sparkfun/SparkFun_Thing_Plus_DA16200/docs/img/hookup_guide/assembly_batt.jpg

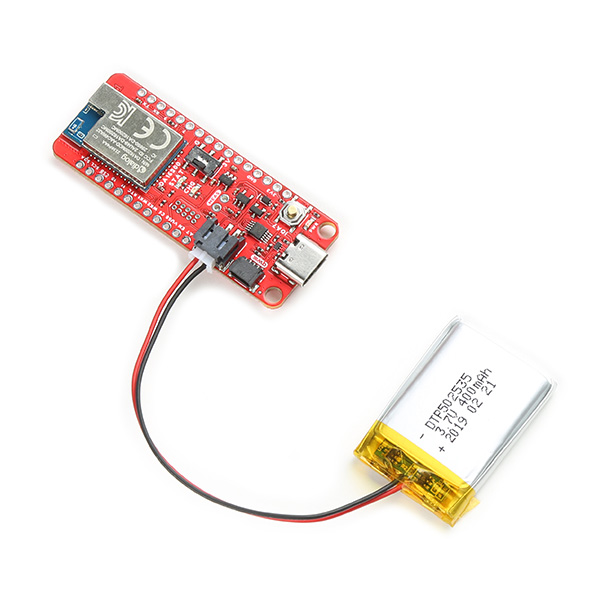
docs/img/hookup_guide/assembly_batt.jpg
