sparkfun/SparkFun_Thing_Plus_DA16200/docs/img/hookup_guide/assembly_headers.jpg

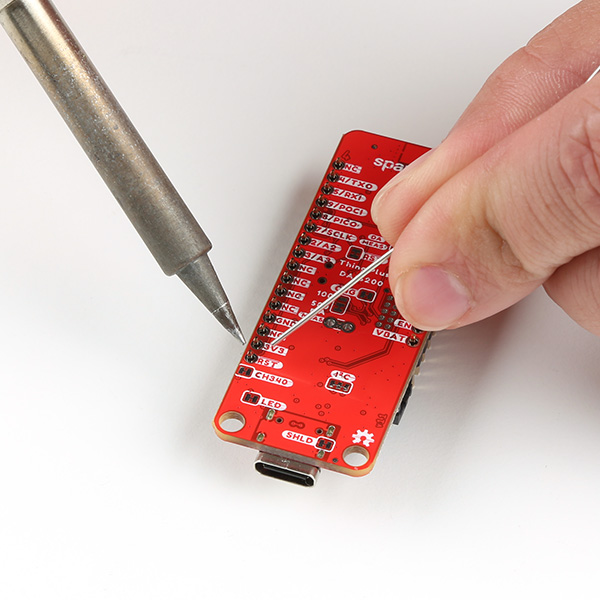
docs/img/hookup_guide/assembly_headers.jpg
