sparkfun/SparkFun_Thing_Plus_DA16200/docs/img/hookup_guide/assembly_jtag_program.jpg

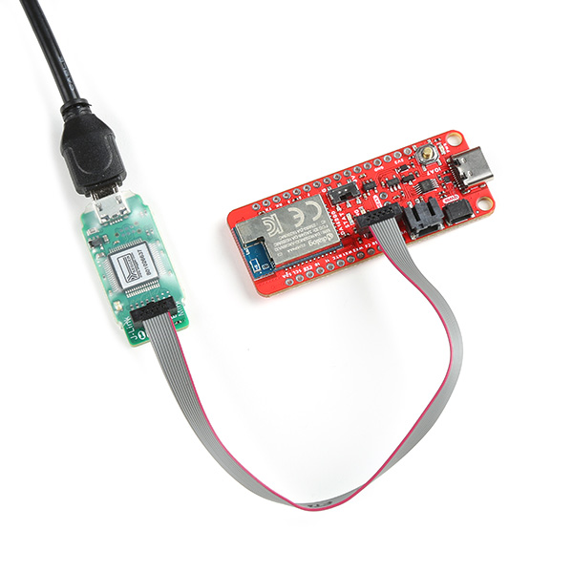
docs/img/hookup_guide/assembly_jtag_program.jpg
