sparkfun/SparkFun_Thing_Plus_DA16200/docs/img/hookup_guide/asssembly_qwiic.jpg

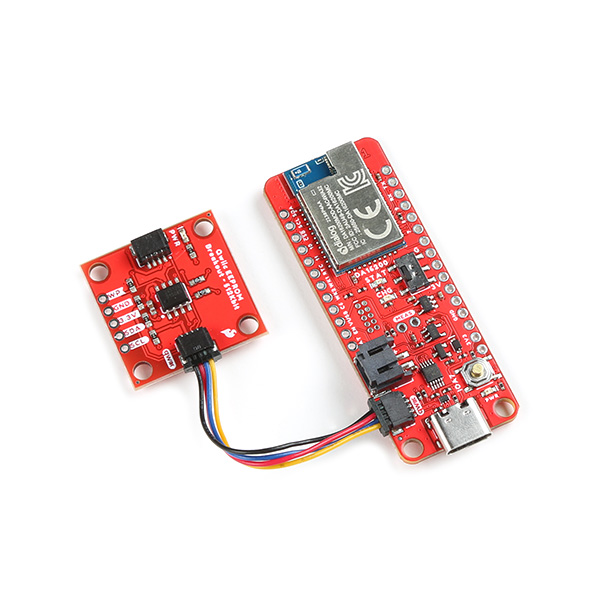
docs/img/hookup_guide/asssembly_qwiic.jpg
