sparkfun/SparkFun_Thing_Plus_DA16200/docs/img/hookup_guide/DA16200- 03.jpg

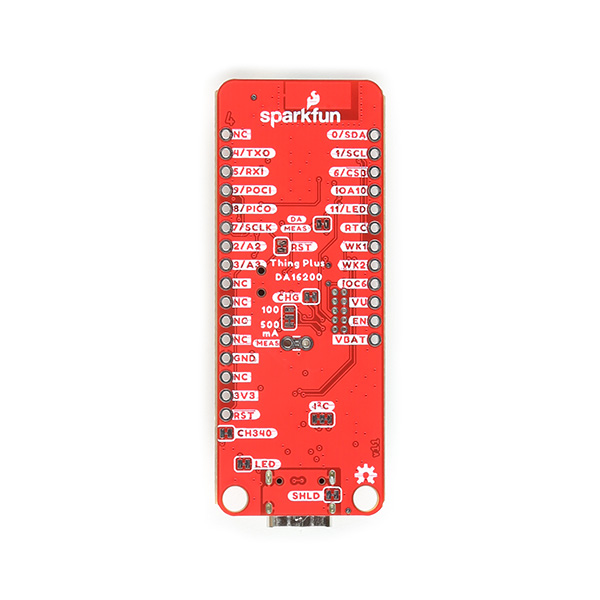
docs/img/hookup_guide/DA16200- 03.jpg
