sparkfun/SparkFun_Thing_Plus_DA16200/docs/img/hookup_guide/DA16200-_02.jpg

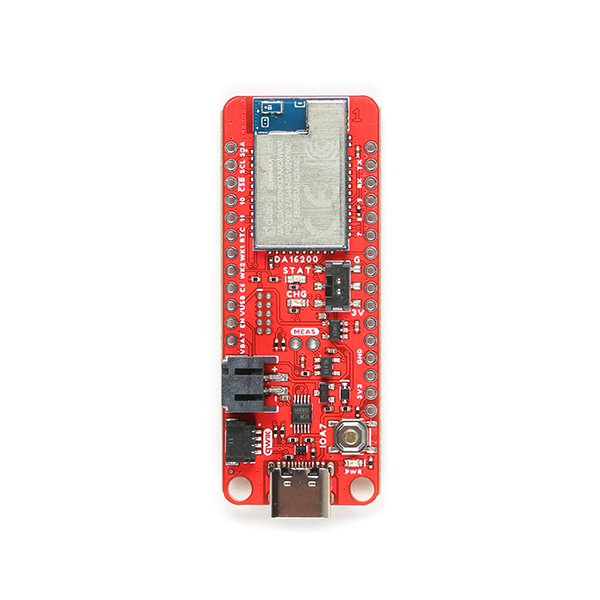
docs/img/hookup_guide/DA16200-_02.jpg
