sparkfun/SparkFun_Thing_Plus_DA16200/docs/img/hookup_guide/DA16200_thing_plus-jumpers.jpg

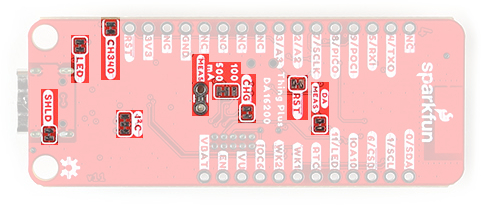
docs/img/hookup_guide/DA16200_thing_plus-jumpers.jpg
