sparkfun/SparkFun_Thing_Plus_DA16200/docs/img/hookup_guide/dimensions.png

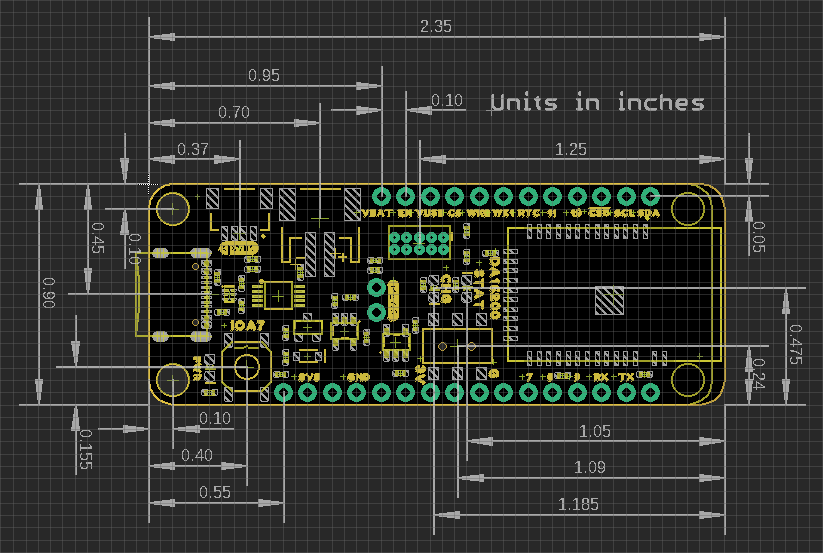
docs/img/hookup_guide/dimensions.png
