sparkfun/SparkFun_Thing_Plus_DA16200/docs/img/hookup_guide/jumper_caution-small.jpg

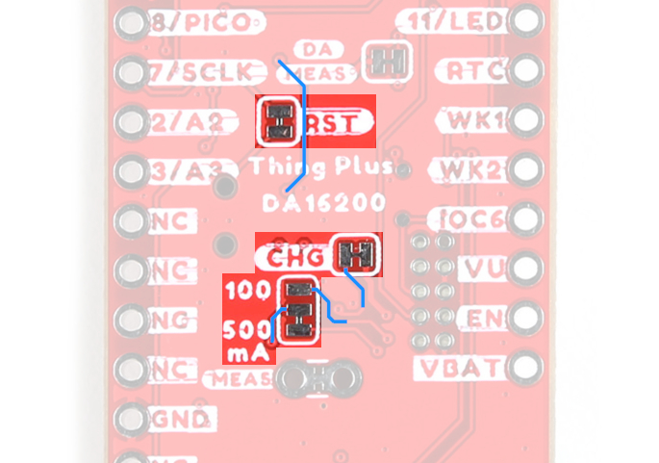
docs/img/hookup_guide/jumper_caution-small.jpg
