sparkfun/SparkFun_Thing_Plus_DA16200/docs/img/sdk_guide/build_project.gif

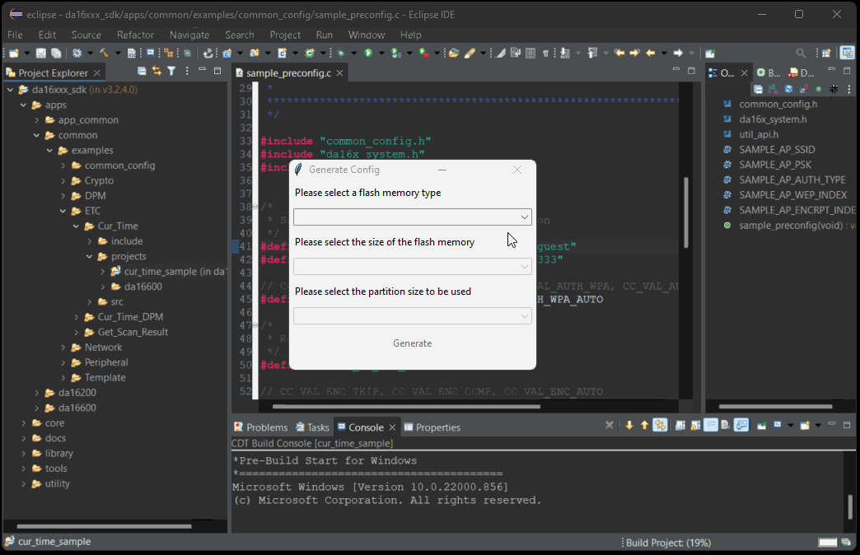
docs/img/sdk_guide/build_project.gif
