sparkfun/SparkFun_Thing_Plus_DA16200/docs/img/sdk_guide/download_firmware.png

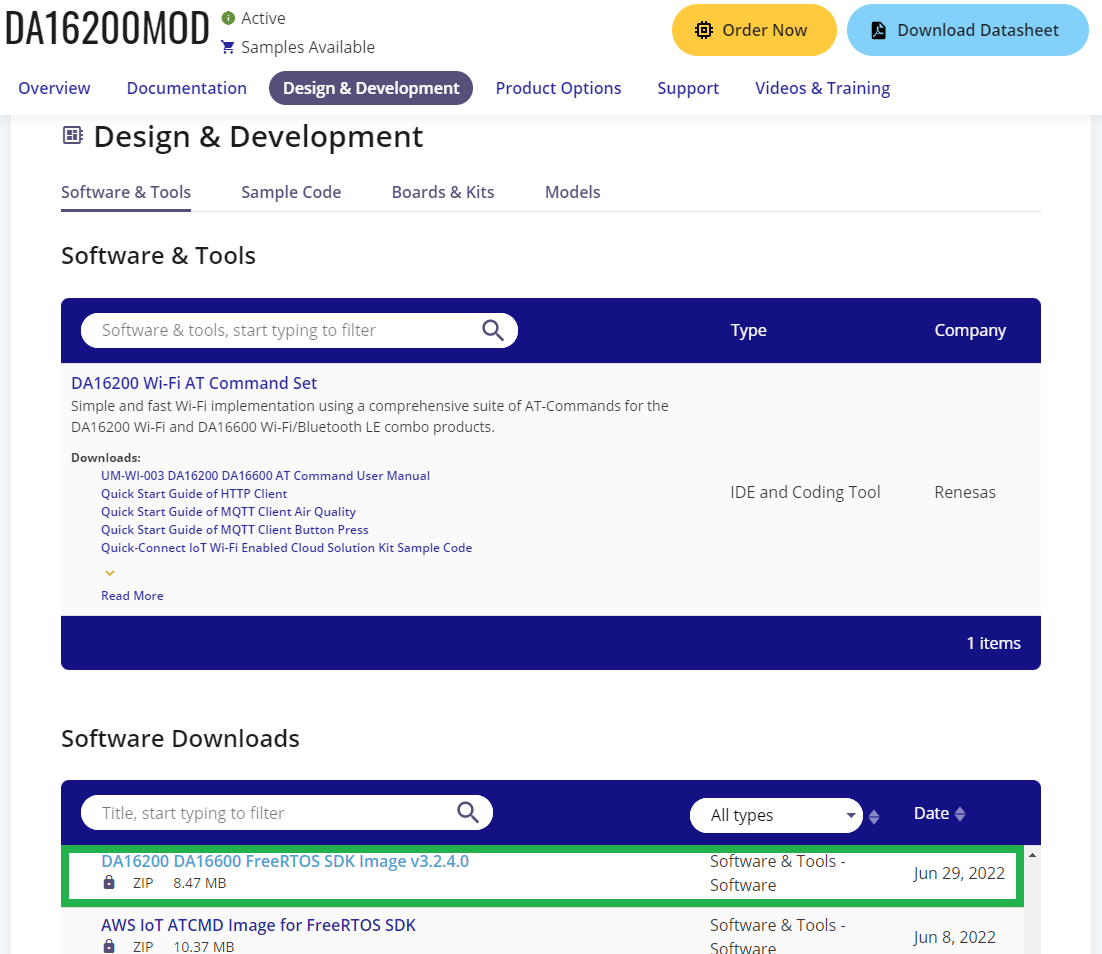
docs/img/sdk_guide/download_firmware.png
