sparkfun/SparkFun_Thing_Plus_DA16200/docs/img/sdk_guide/eclipse-config_wifi.png

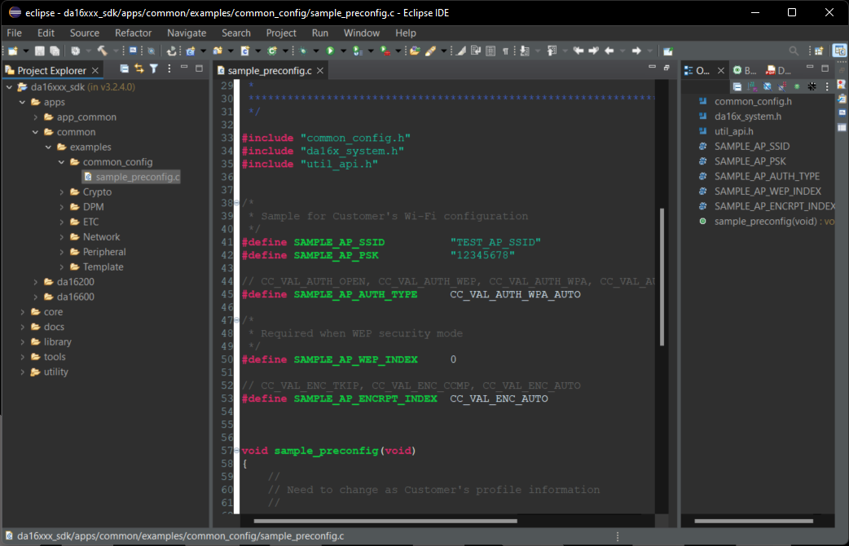
docs/img/sdk_guide/eclipse-config_wifi.png
