sparkfun/SparkFun_Thing_Plus_DA16200/docs/img/sdk_guide/eclipse-gpio_project_folder.png

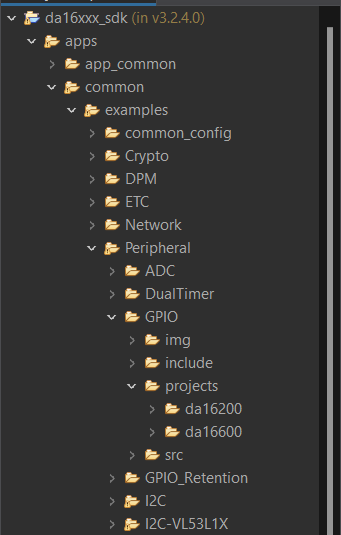
docs/img/sdk_guide/eclipse-gpio_project_folder.png
