sparkfun/SparkFun_Thing_Plus_DA16200/docs/img/sdk_guide/eclipse-import_projects-root_directory-folder.png

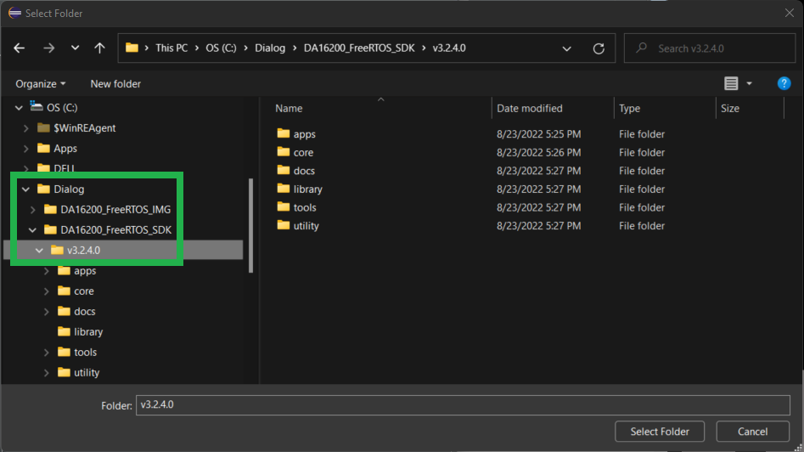
docs/img/sdk_guide/eclipse-import_projects-root_directory-folder.png
