sparkfun/SparkFun_Thing_Plus_DA16200/docs/img/sdk_guide/eclipse-import_projects-root_directory.png

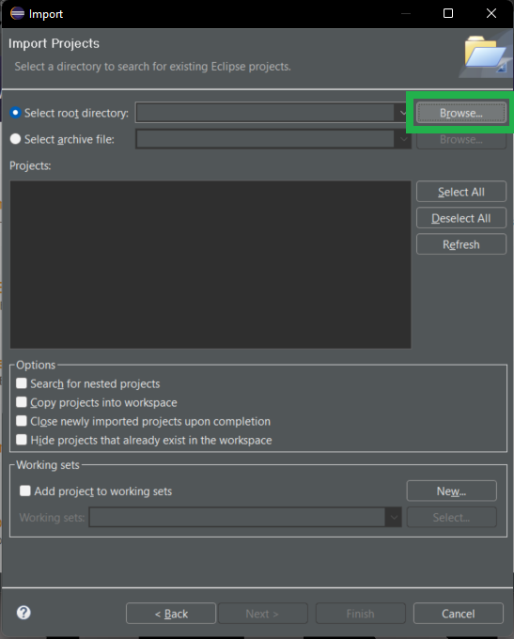
docs/img/sdk_guide/eclipse-import_projects-root_directory.png
