sparkfun/SparkFun_Thing_Plus_DA16200/docs/img/sdk_guide/eclipse-jlink2.png

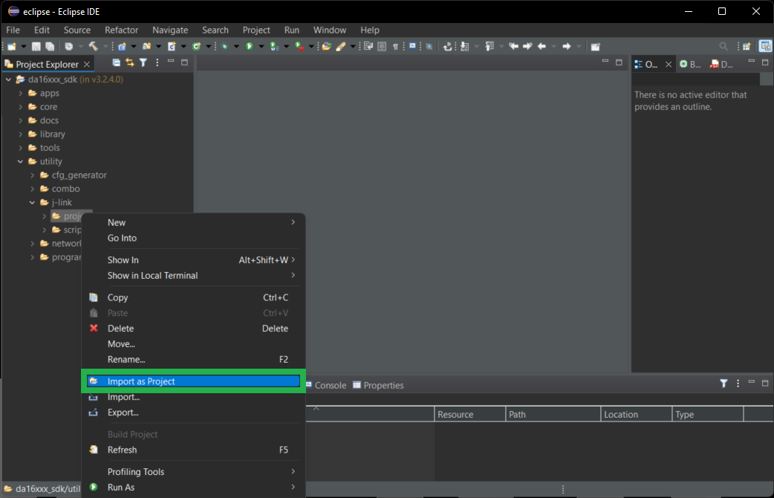
docs/img/sdk_guide/eclipse-jlink2.png
