sparkfun/SparkFun_Thing_Plus_DA16200/docs/img/sdk_guide/eclipse-preferences-arm_toolchain.png

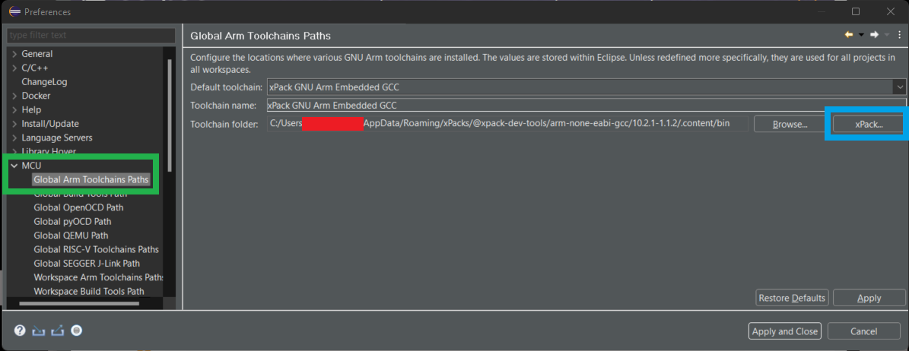
docs/img/sdk_guide/eclipse-preferences-arm_toolchain.png
