sparkfun/SparkFun_Thing_Plus_DA16200/docs/img/sdk_guide/eclipse-preferences-build_tools.png

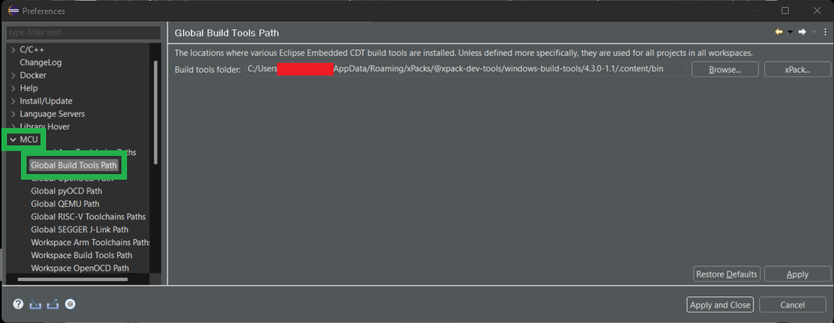
docs/img/sdk_guide/eclipse-preferences-build_tools.png
