sparkfun/SparkFun_Thing_Plus_DA16200/docs/img/sdk_guide/eclipse-preferences_string_substitution.png

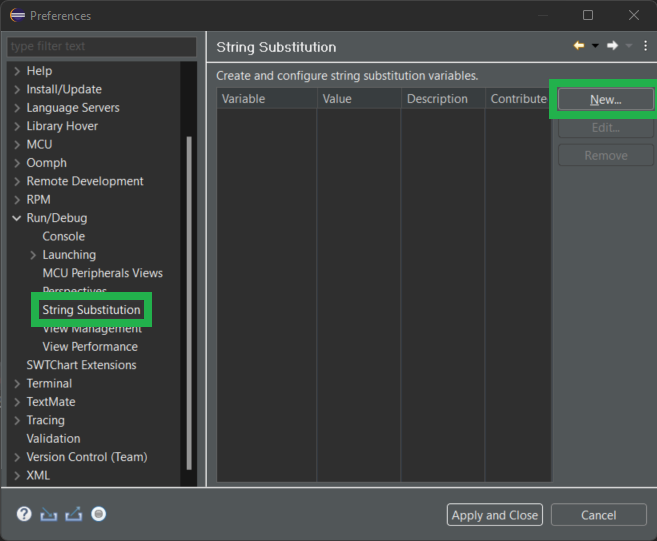
docs/img/sdk_guide/eclipse-preferences_string_substitution.png
