sparkfun/SparkFun_Thing_Plus_DA16200/docs/img/sdk_guide/eclipse-preferences_string_substitution_new_variable.png

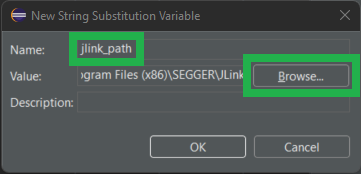
docs/img/sdk_guide/eclipse-preferences_string_substitution_new_variable.png
