sparkfun/SparkFun_Thing_Plus_DA16200/docs/img/sdk_guide/eclipse-program_j-link.png

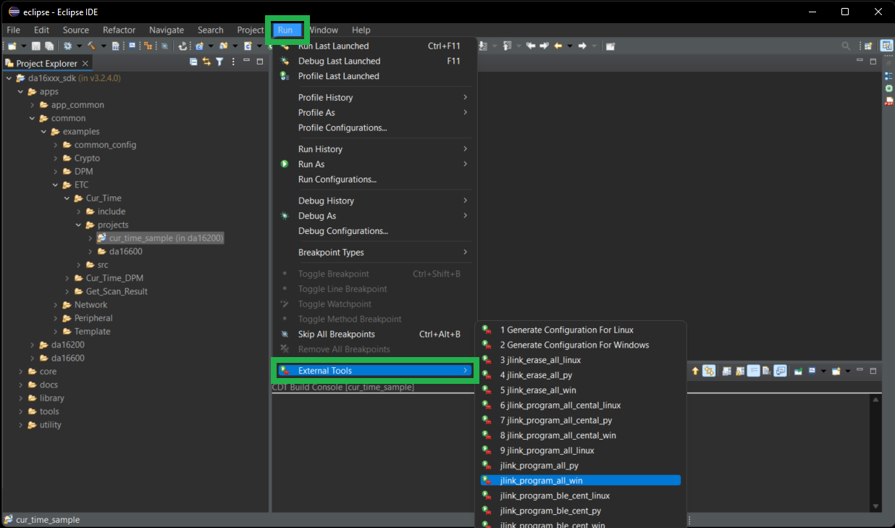
docs/img/sdk_guide/eclipse-program_j-link.png
