sparkfun/SparkFun_Thing_Plus_DA16200/docs/img/sdk_guide/eclipse-project_explorer.png

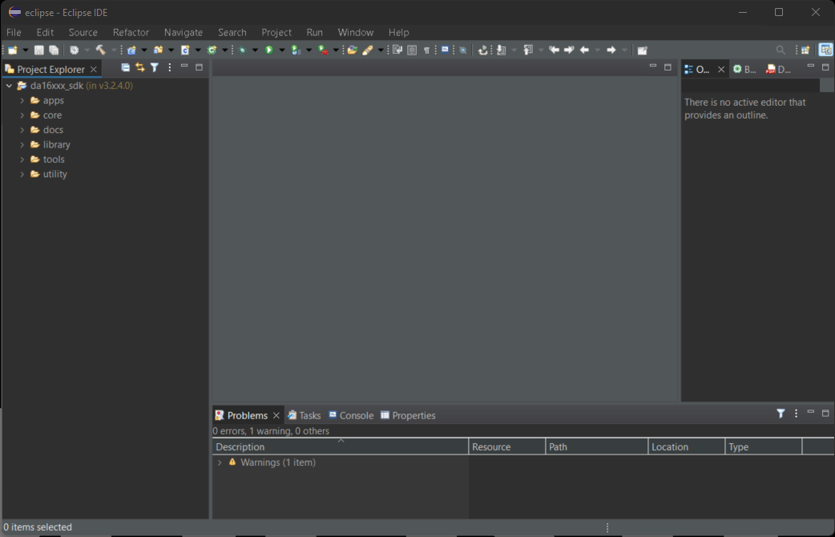
docs/img/sdk_guide/eclipse-project_explorer.png
