sparkfun/SparkFun_Thing_Plus_DA16200/docs/img/sdk_guide/eclipse-sdk-build_version_number.png

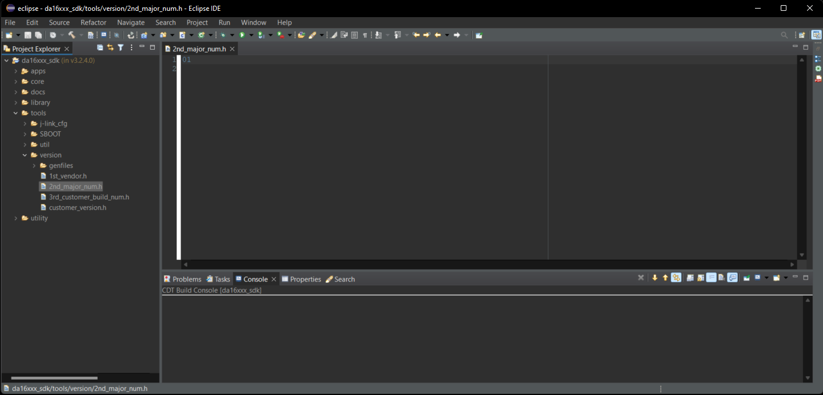
docs/img/sdk_guide/eclipse-sdk-build_version_number.png
