sparkfun/SparkFun_Thing_Plus_DA16200/docs/img/sdk_guide/eclipse-sdk_examples-build_project.png

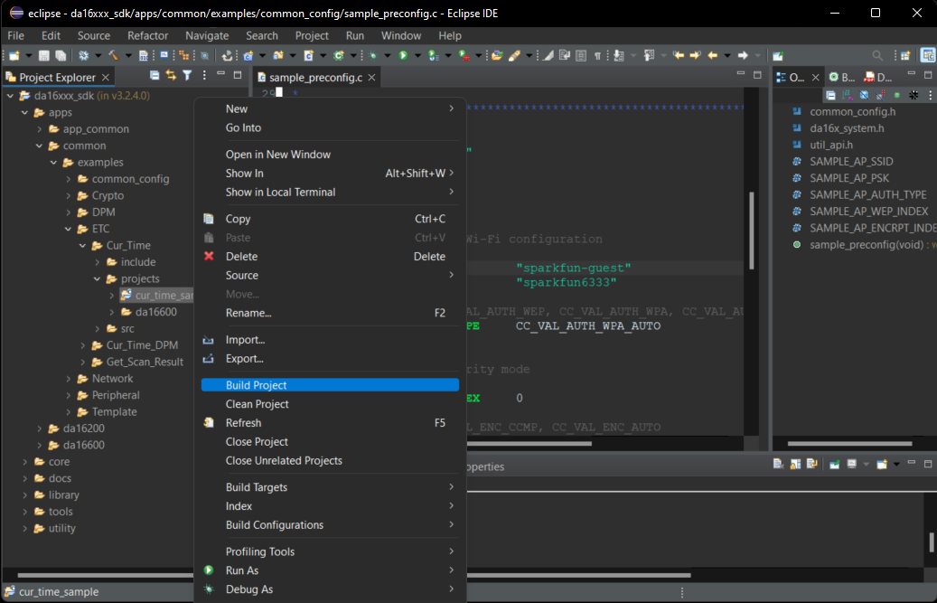
docs/img/sdk_guide/eclipse-sdk_examples-build_project.png
