sparkfun/SparkFun_Thing_Plus_DA16200/docs/img/sdk_guide/eclipse-sdk_examples-firmware_images.png

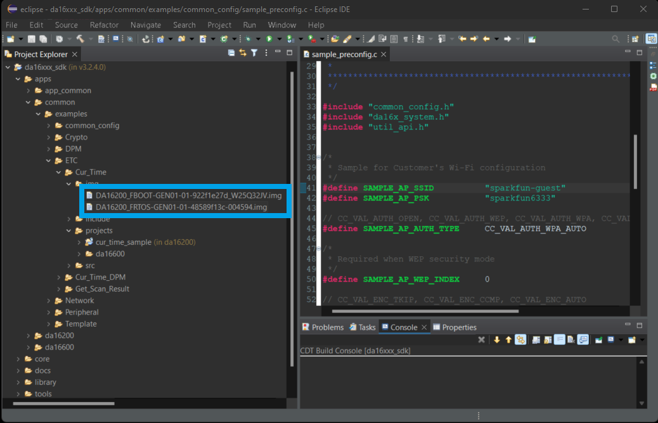
docs/img/sdk_guide/eclipse-sdk_examples-firmware_images.png
