sparkfun/SparkFun_Thing_Plus_DA16200/docs/img/sdk_guide/eclipse-sdk_examples-import_project.png

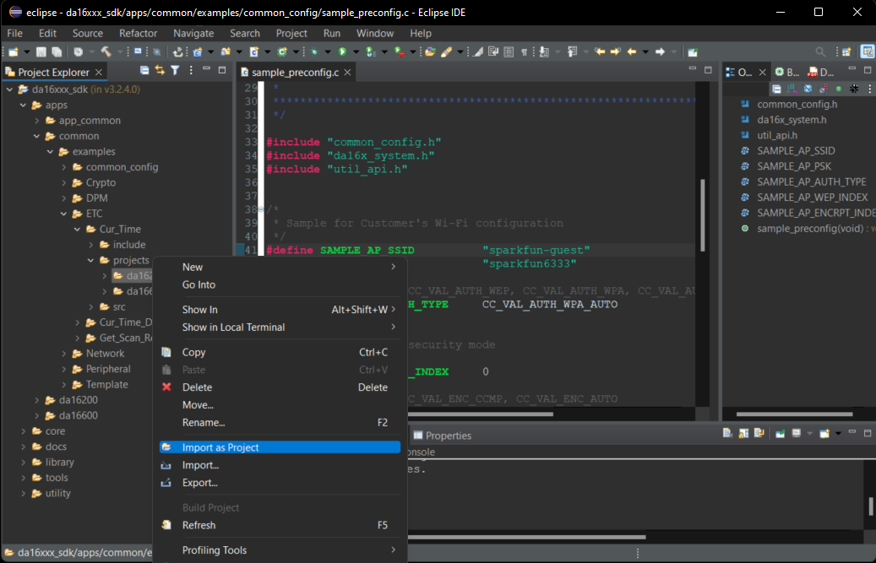
docs/img/sdk_guide/eclipse-sdk_examples-import_project.png
