sparkfun/SparkFun_Thing_Plus_DA16200/docs/img/sdk_guide/eclipse-window_menu-preferences.png

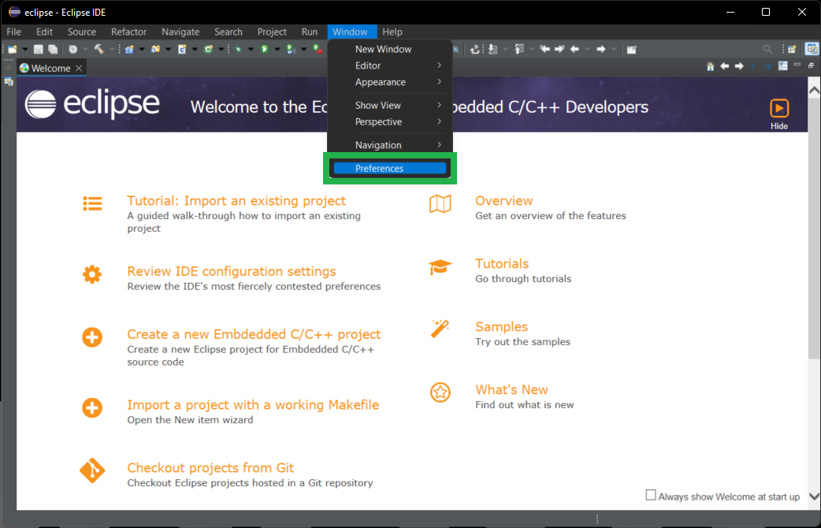
docs/img/sdk_guide/eclipse-window_menu-preferences.png
