sparkfun/SparkFun_Thing_Plus_DA16200/docs/img/sdk_guide/eclipse_installer2.png

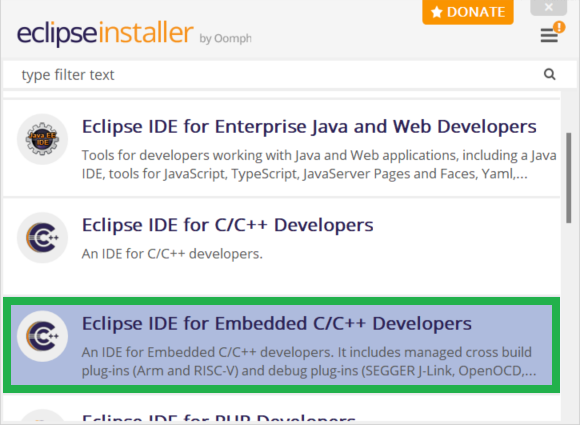
docs/img/sdk_guide/eclipse_installer2.png
