sparkfun/SparkFun_Thing_Plus_DA16200/docs/img/sdk_guide/firmware_update_macro.gif

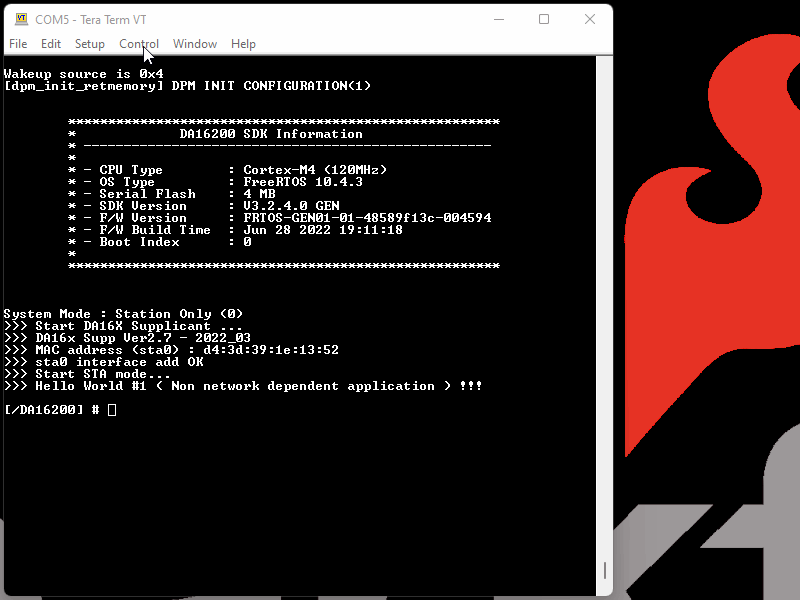
docs/img/sdk_guide/firmware_update_macro.gif
