sparkfun/SparkFun_Thing_Plus_DA16200/docs/img/sdk_guide/j-link_flash_loader_files.png

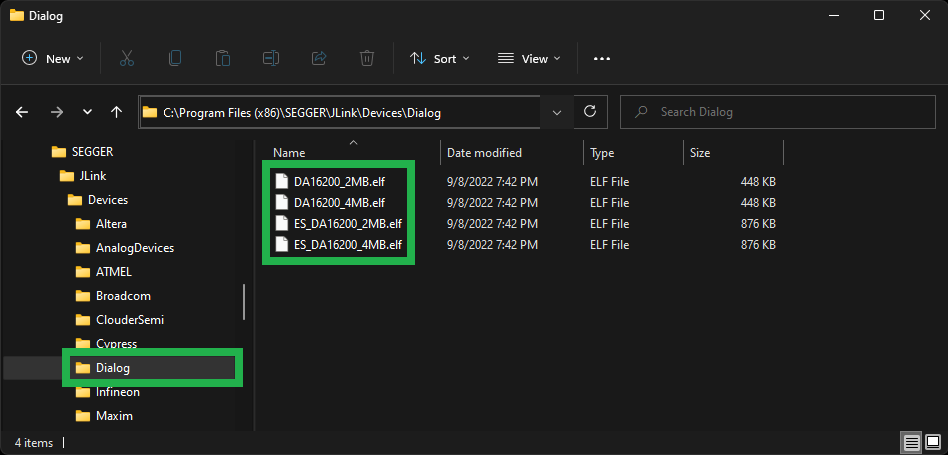
docs/img/sdk_guide/j-link_flash_loader_files.png
