sparkfun/SparkFun_Thing_Plus_DA16200/docs/img/sdk_guide/j-link_jlinkdevices_file.png

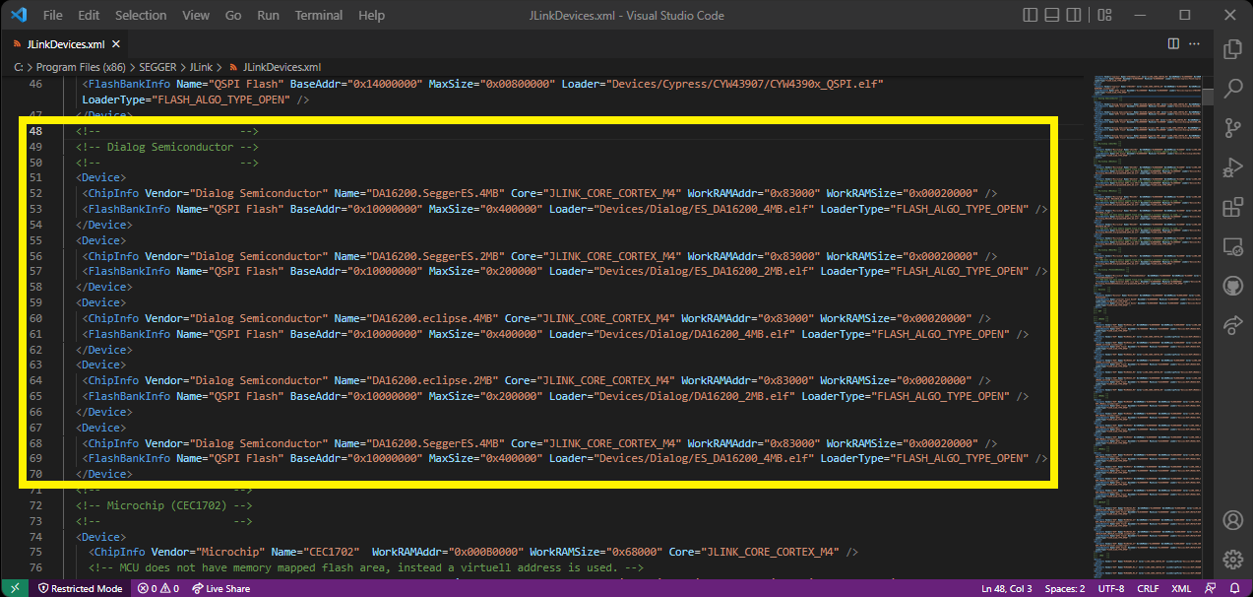
docs/img/sdk_guide/j-link_jlinkdevices_file.png
