sparkfun/SparkFun_Thing_Plus_DA16200/docs/img/sdk_guide/sdk_root_directory2.png

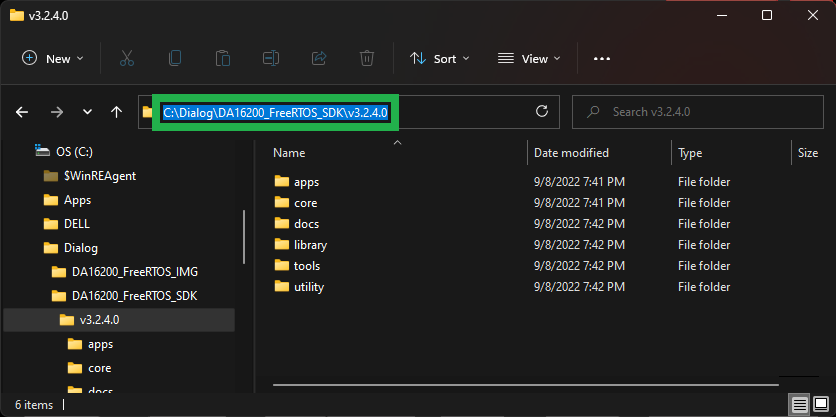
docs/img/sdk_guide/sdk_root_directory2.png
