sparkfun/SparkFun_Thing_Plus_DA16200/docs/img/sdk_guide/sdk_root_directory.png

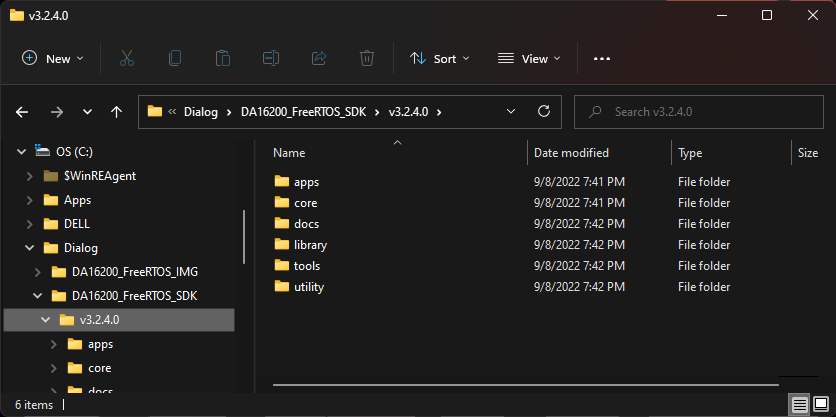
docs/img/sdk_guide/sdk_root_directory.png
