sparkfun/SparkFun_Thing_Plus_DA16200/docs/img/sdk_guide/select_boot_img.png

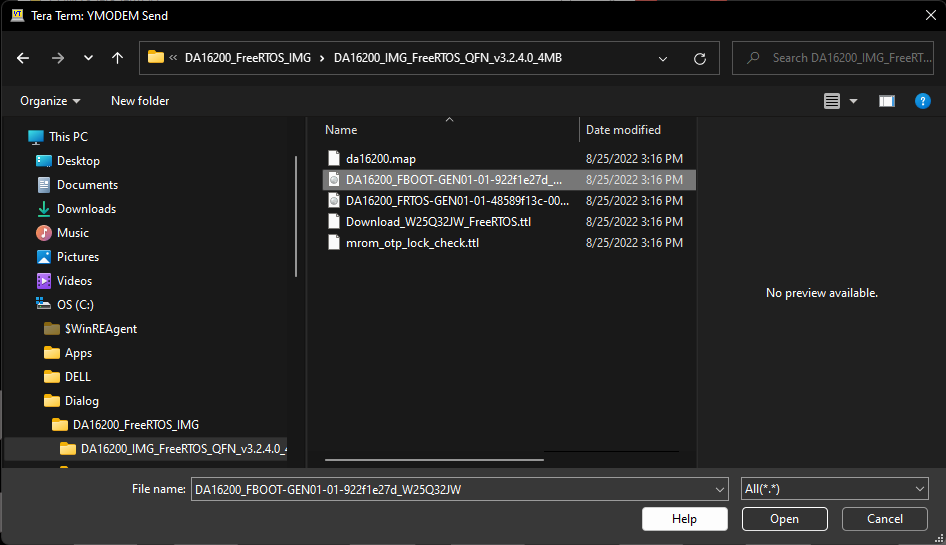
docs/img/sdk_guide/select_boot_img.png
