sparkfun/SparkFun_Thing_Plus_DA16200/docs/img/sdk_guide/tera_term-factory_reset_success.png

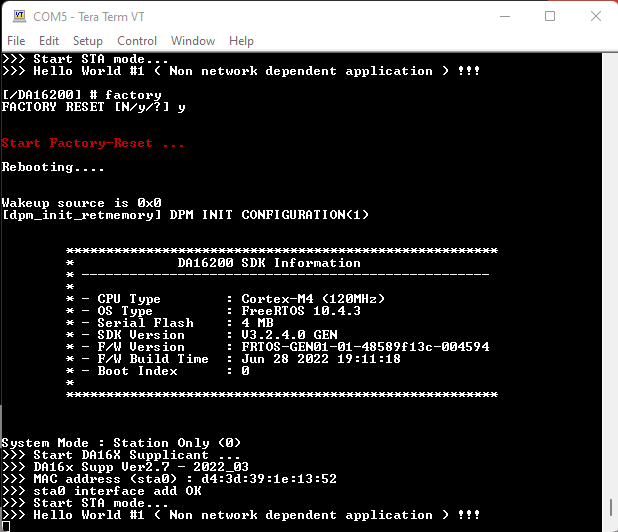
docs/img/sdk_guide/tera_term-factory_reset_success.png
