sparkfun/SparkFun_Thing_Plus_DA16200/docs/img/sdk_guide/tera_term-firmware_transfer_successful.png

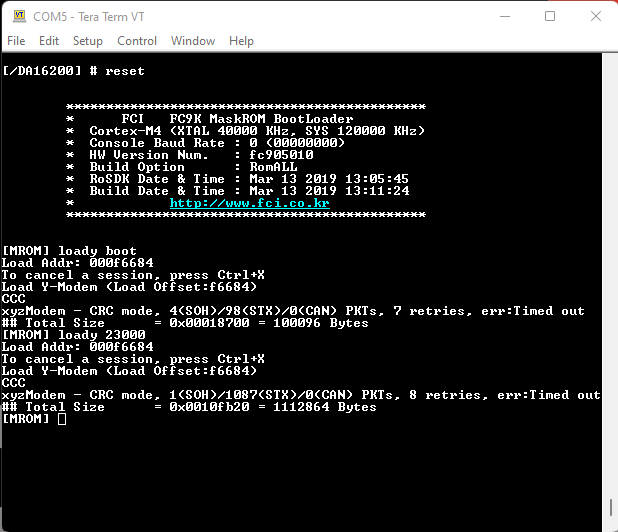
docs/img/sdk_guide/tera_term-firmware_transfer_successful.png
