sparkfun/SparkFun_Thing_Plus_DA16200/docs/img/sdk_guide/tera_term-mrom_command_mode2.png

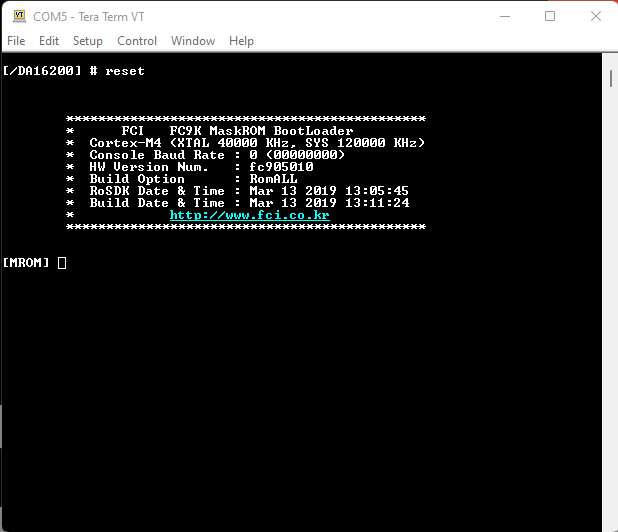
docs/img/sdk_guide/tera_term-mrom_command_mode2.png
