sparkfun/SparkFun_Thing_Plus_DA16200/docs/img/sdk_guide/tera_term-y-modem_send.png

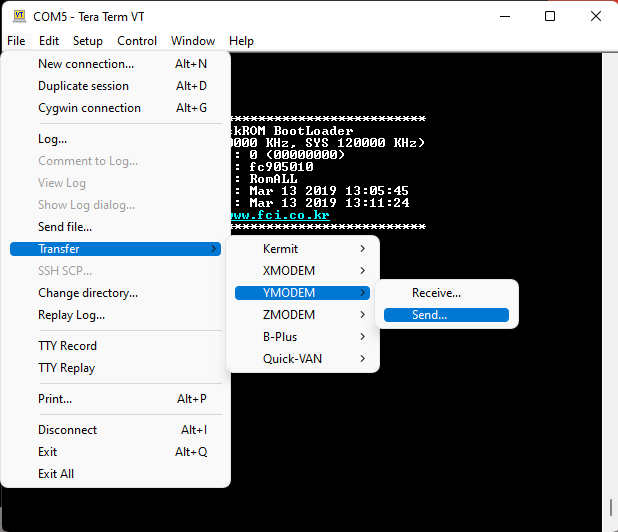
docs/img/sdk_guide/tera_term-y-modem_send.png
