sparkfun/SparkFun_Thing_Plus_DA16200/docs/img/sdk_guide/terminal-Cur_Time.gif

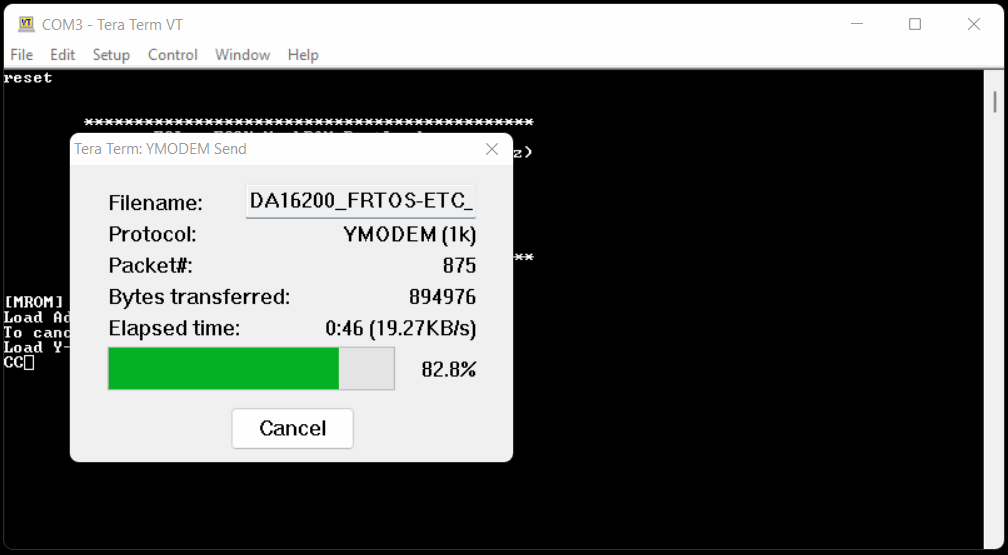
docs/img/sdk_guide/terminal-Cur_Time.gif
