sparkfun/SparkFun_Thing_Plus_DA16200/docs/img/sdk_guide/terminal-I2C_EEPROM.png

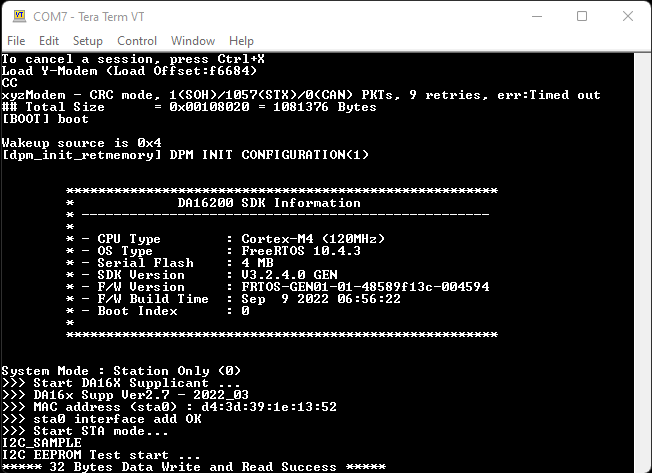
docs/img/sdk_guide/terminal-I2C_EEPROM.png
