sparkfun/SparkFun_Thing_Plus_DA16200/docs/img/sdk_guide/terminal-wifi_config.gif

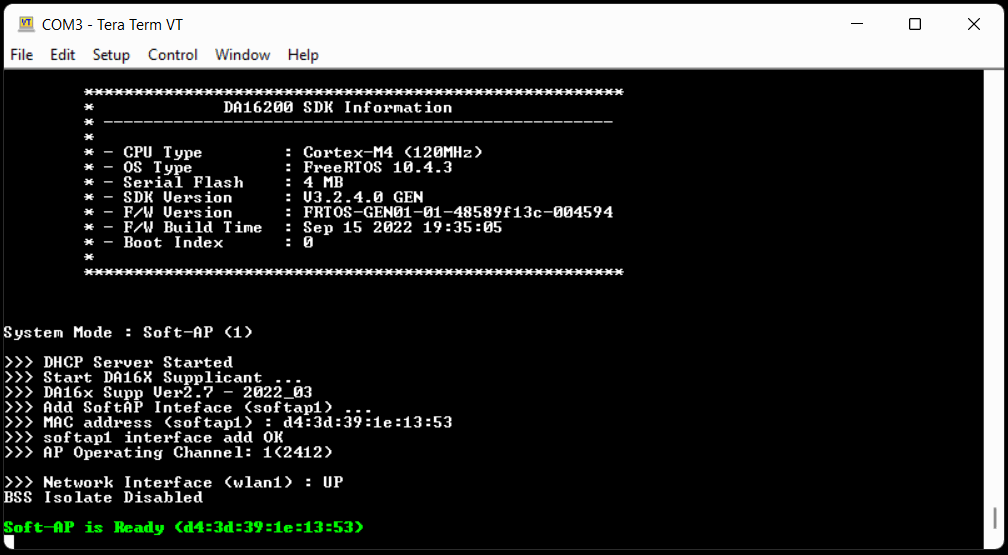
docs/img/sdk_guide/terminal-wifi_config.gif
