sparkfun/SparkFun_Thing_Plus_DA16200/docs/img/sdk_guide/thumbnail/238571.png

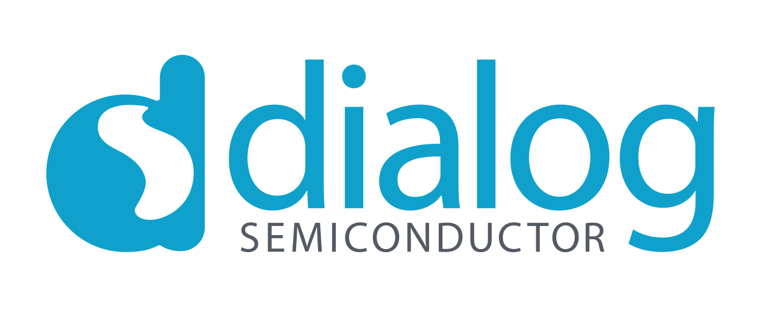
docs/img/sdk_guide/thumbnail/238571.png
