sparkfun/SparkFun_Thing_Plus_DA16200/docs/img/sdk_guide/thumbnail/renesas-top-740x375.jpg

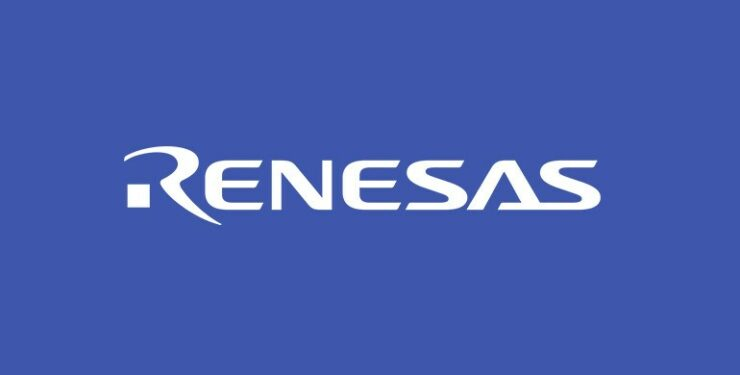
docs/img/sdk_guide/thumbnail/renesas-top-740x375.jpg
