sparkfun/SparkFun_Thing_Plus_DA16200/docs/img/sdk_guide/y-modem-boot_transfer.png

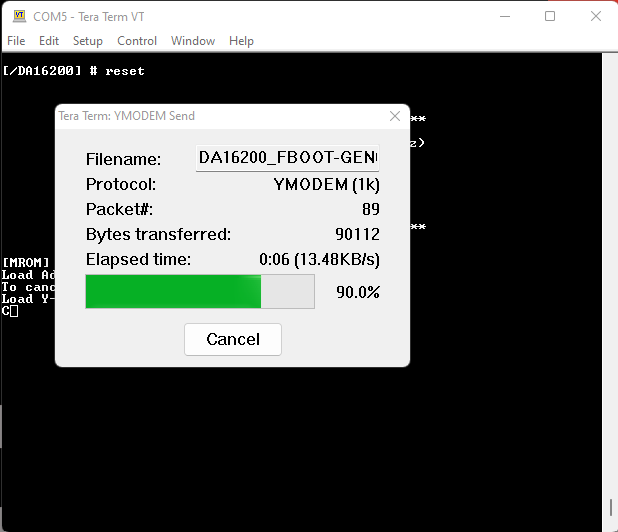
docs/img/sdk_guide/y-modem-boot_transfer.png
