sparkfun/SparkFun_Thing_Plus_DA16200/docs/img/sdk_guide/eclipse-select_debug_mode.png

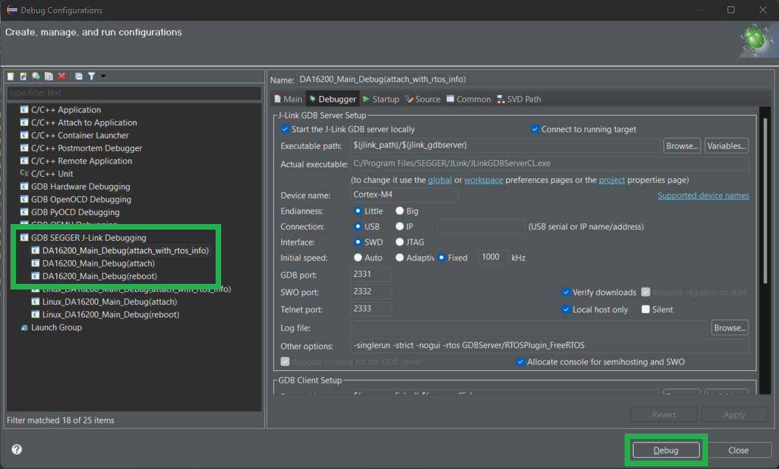
docs/img/sdk_guide/eclipse-select_debug_mode.png
